LeandroBenitez12/SAMI-SUMO/Software/PruebaMotores.ino

#include <SumoEngineController.h>
// Variables y constantes para los motores
#define PIN_ENGINE_DIR_RIGHT 22 //DIR
#define PIN_ENGINE_PWM_RIGHT 21 //PWM
#define PIN_ENGINE_DIR_LEFT 19 //DIR
#define PIN_ENGINE_PWM_LEFT 18 //PWM
int rightSpeed = 100;
int leftSpeed = 100;

EngineController *sami = new EngineController(PIN_ENGINE_DIR_RIGHT, PIN_ENGINE_PWM_RIGHT, PIN_ENGINE_DIR_LEFT, PIN_ENGINE_PWM_LEFT);

void setup(){

}

void loop(){
    sami->Forward(rightSpeed, leftSpeed);
    delay(3000);
    sami->Backward(rightSpeed, leftSpeed);
    delay(3000);
    sami->Right(rightSpeed, leftSpeed);
    delay(3000);
    sami->Left(rightSpeed, leftSpeed);
    delay(3000);
    sami->Stop();
    delay(3000);
}
